mnemocron/my-discrete-fpga/sketch/diyfpga-compile/generate_vhdl_stimuli.c

/*******************************************************************************
 * @file        create_vhdl_stimuli.c
 * @brief       Compiles the program in diyfpga_user.c to a bitstream readable
 *              by the VHDL testbench
 * @details     
 * @version     
 * @author      Simon Burkhardt https://github.com/mnemocron
 * @date        2024.04
 * @see         https://github.com/mnemocron/my-discrete-fpga
*******************************************************************************/
#if !defined(__AVR_ATmega328P__) // exclude everything for the Arduino compiler

#include <stdio.h>
#include "diyfpga.h"
#include "diyfpga_user.h"

fpga_t myfpga;

void create_bitstream_txt(char* bit, int len);

int main()
{
    printf("compiling...\n");
    /* Program the FPGA functionality in myfpga_user.cpp */
    diyfpga_setup(); 
    create_bitstream(&myfpga);
    create_bitstream_txt(myfpga.bitstream, N_BYTES_BITSTREAM);
    printf("Successfully written ./bitstream.txt\n");

    return 0;
}

void create_bitstream_txt(char* bit, int len){
  FILE *fptr;
  fptr = fopen("bitstream.txt", "w");
  for(int i=0; i<len; i++)
    fprintf(fptr, BYTE_TO_BINARY_PATTERN"\n", BYTE_TO_BINARY(bit[i]));
  fclose(fptr);
}

#endif
